afourney/usb-k1-speakermic-adapter/pcb/preview/3d-bottom.png

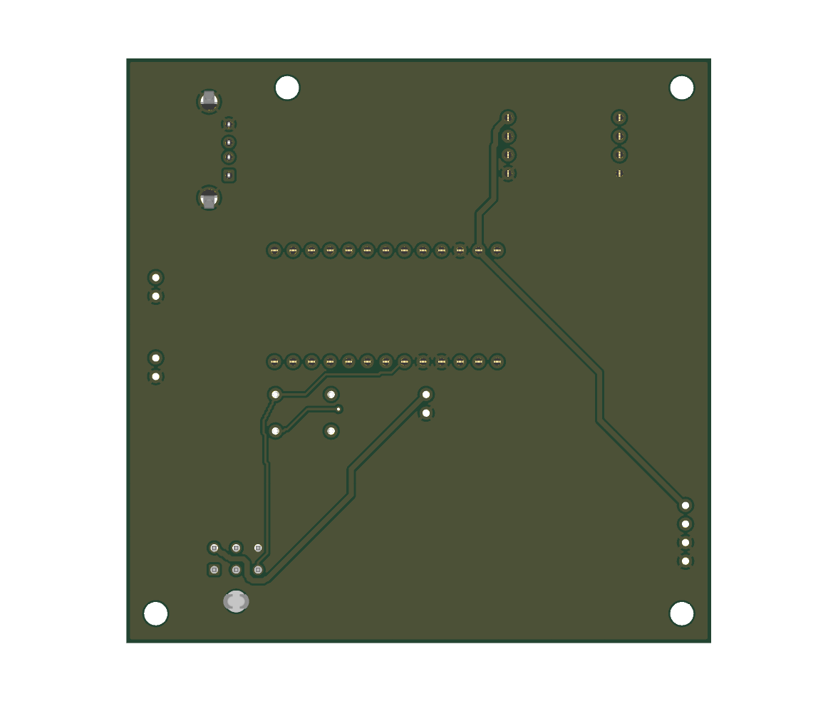
pcb/preview/3d-bottom.png
