afourney/usb-k1-speakermic-adapter/pcb/preview/3d.png

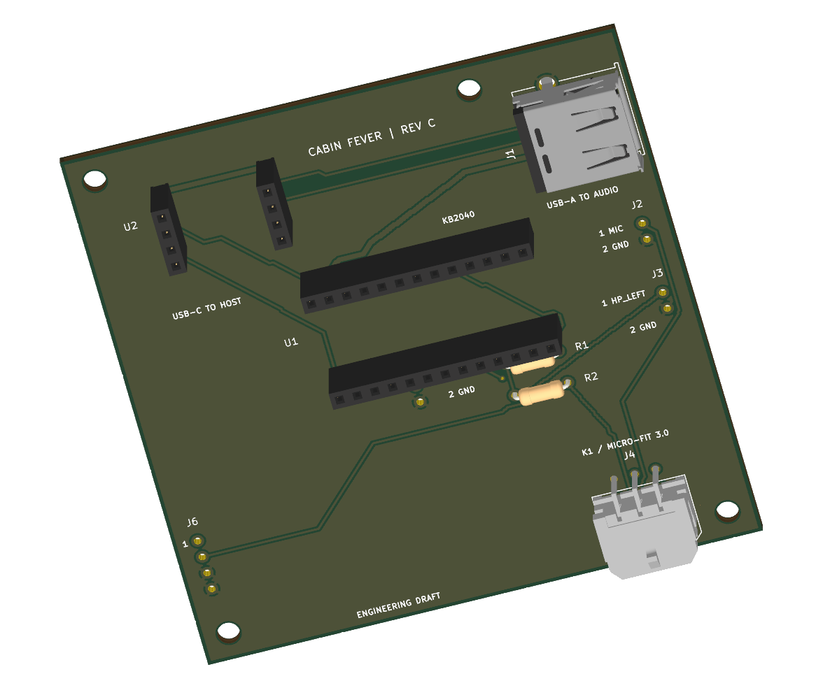
pcb/preview/3d.png
