afourney/usb-k1-speakermic-adapter/pcb/references/lm386-connections.jpg

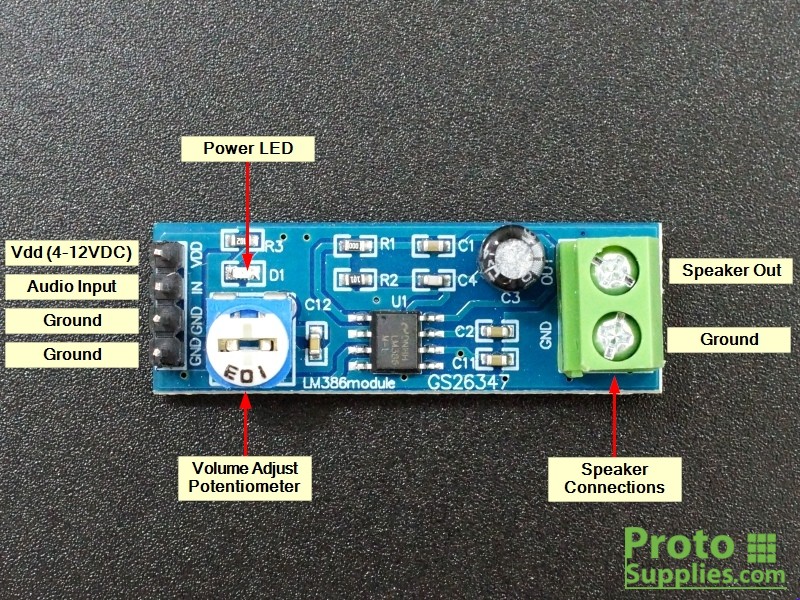
pcb/references/lm386-connections.jpg
